Tendo33/LI-FI/Code récepteur LIFI/System/sys/stm32_system.c

#include "stm32_system.h"

/*******************************************************************************
* Function Name  : SystemClock_Init
* Description    : STM32F7时钟配置
* Input          : Fosc: 输入晶振频率,单位MHz
* Output         : None
* Return         : None
* Note			 : Fvco=Fs*(plln/pllm),VCO时钟频率
				   Fsys=Fvco/pllp, MCU系统时钟频率,这里为216MHz
				   Fusb=Fvco/pllq, USB,SDIO,RNG时钟频率,必须为48MHz
				   PLLN:主PLL倍频系数(PLL倍频),取值范围:192~432
				   PLLM:主PLL和音频PLL分频系数(PLL之前的分频),取值范围:2~63
				   PLLP:系统时钟的主PLL分频系数(PLL之后的分频),取值范围:2,4,6,8.(仅限这4个值)
				   PLLQ:USB/SDIO/随机数产生器等的主PLL分频系数(PLL之后的分频),取值范围:2~15
				   Fs:晶振输入(4-26MHz)(HSE)
*******************************************************************************/
void SystemClock_Init(u8 Fosc)
{
	RCC_ClkInitTypeDef RCC_ClkInitStruct;
	RCC_OscInitTypeDef RCC_OscInitStruct;
	HAL_StatusTypeDef ret = HAL_OK;

	/* Enable HSE Oscillator and activate PLL with HSE as source */
	RCC_OscInitStruct.OscillatorType = RCC_OSCILLATORTYPE_HSE;
	RCC_OscInitStruct.HSEState = RCC_HSE_ON;
	RCC_OscInitStruct.PLL.PLLState = RCC_PLL_ON;
	RCC_OscInitStruct.PLL.PLLSource = RCC_PLLSOURCE_HSE;
	RCC_OscInitStruct.PLL.PLLM = Fosc;
	RCC_OscInitStruct.PLL.PLLN = 432;  
	RCC_OscInitStruct.PLL.PLLP = RCC_PLLP_DIV2;
	RCC_OscInitStruct.PLL.PLLQ = 9;

	ret = HAL_RCC_OscConfig(&RCC_OscInitStruct);
	if(ret != HAL_OK)
	{
		while(1) { ; }
	}

	/* Activate the OverDrive to reach the 216 MHz Frequency */  
	ret = HAL_PWREx_EnableOverDrive();
	if(ret != HAL_OK)
	{
		while(1) { ; }
	}

	/* Select PLL as system clock source and configure the HCLK, PCLK1 and PCLK2 clocks dividers */
	RCC_ClkInitStruct.ClockType = (RCC_CLOCKTYPE_SYSCLK | RCC_CLOCKTYPE_HCLK | RCC_CLOCKTYPE_PCLK1 | RCC_CLOCKTYPE_PCLK2);
	RCC_ClkInitStruct.SYSCLKSource = RCC_SYSCLKSOURCE_PLLCLK;
	RCC_ClkInitStruct.AHBCLKDivider = RCC_SYSCLK_DIV1;
	RCC_ClkInitStruct.APB1CLKDivider = RCC_HCLK_DIV4;  
	RCC_ClkInitStruct.APB2CLKDivider = RCC_HCLK_DIV2; 

	ret = HAL_RCC_ClockConfig(&RCC_ClkInitStruct, FLASH_LATENCY_7);
	if(ret != HAL_OK)
	{
		while(1) { ; }
	}  
}

/*******************************************************************************
* Function Name  : MPU_Config
* Description    : Configure the MPU attributes as Write Through for SRAM1/2
* Input          : None
* Output         : None
* Return         : None
* Note			 : The Base Address is 0x20010000 since this memory interface is the AXI.
         	       The Region Size is 256KB, it is related to SRAM1 and SRAM2  memory size.
*******************************************************************************/
void MPU_Config(void)
{
	MPU_Region_InitTypeDef MPU_InitStruct;

	/* Disable the MPU */
	HAL_MPU_Disable();

	/* Configure the MPU attributes as WT for SRAM */
	MPU_InitStruct.Enable = MPU_REGION_ENABLE;
	MPU_InitStruct.BaseAddress = 0x20010000;
	MPU_InitStruct.Size = MPU_REGION_SIZE_256KB;
	MPU_InitStruct.AccessPermission = MPU_REGION_FULL_ACCESS;
	MPU_InitStruct.IsBufferable = MPU_ACCESS_NOT_BUFFERABLE;
	MPU_InitStruct.IsCacheable = MPU_ACCESS_CACHEABLE;
	MPU_InitStruct.IsShareable = MPU_ACCESS_NOT_SHAREABLE;
	MPU_InitStruct.Number = MPU_REGION_NUMBER0;
	MPU_InitStruct.TypeExtField = MPU_TEX_LEVEL0;
	MPU_InitStruct.SubRegionDisable = 0x00;
	MPU_InitStruct.DisableExec = MPU_INSTRUCTION_ACCESS_ENABLE;

	HAL_MPU_ConfigRegion(&MPU_InitStruct);

	/* Enable the MPU */
	HAL_MPU_Enable(MPU_PRIVILEGED_DEFAULT);
}

/*******************************************************************************
* Function Name  : CPU_CACHE_Enable
* Description    : STM32F7的L1-Cache使能
* Input          : None
* Output         : None
* Return         : None
* Note			 : None
*******************************************************************************/
void CPU_CACHE_Enable(void)
{
	/* Enable I-Cache */
	SCB_EnableICache();

	/* Enable D-Cache */
	SCB_EnableDCache();
}

/*******************************************************************************
* Function Name  : NVIC_Config
* Description    : NVIC中断配置
* Input          : IRQn:中断号
				   PriorityGroup：优先级分组
				   priority：优先级
* Output         : None
* Return         : None
* Note			 : 调用函数定义在core_cm7.h中, 注意所有中断的优先级分组是一样的
				   优先级分组时针对所有的中断的,此函数是针对外设中断的，不包括
				   系统中断,SysTick
*******************************************************************************/
void NVIC_Config(IRQn_Type IRQn, uint32_t PriorityGroup, uint32_t priority)
{
	NVIC_SetPriorityGrouping(PriorityGroup); //设置中断分组
	NVIC_SetPriority(IRQn, priority);	     //设置中断优先级
	NVIC_EnableIRQ(IRQn);	                 //使能中断
}

//系统软复位   
void Sys_Soft_Reset(void)
{   
	SCB->AIRCR =0X05FA0000|(u32)0x04;	  
}

/*******************************************************************************
* Function Name  : System_Init
* Description    : 系统初始化
* Input          : None
* Output         : None
* Return         : None
* Note			 : None
*******************************************************************************/
void System_Init(void)
{
	/* Configure the MPU attributes as Write Through */
	MPU_Config();

	/* Enable the CPU Cache */
	CPU_CACHE_Enable();
	
	HAL_Init();             //其中配置了SYSTICK,时间为1ms,库函数要用到,这里,我们会重新定义
	SystemClock_Init(FOSC);
}
