Tendo33/LI-FI/Code récepteur LIFI/User/MyIncludes.h

#ifndef __MYINCLUDES_H_
#define __MYINCLUDES_H_

#include "stm32f7xx.h"
#include "stm32_types.h"
#include "stm32_system.h"
#include "delay.h"

#include "string.h"
#include "Timerx.h"
#include "sensor.h"


#endif
